GQster/catLaserPointer/SolidworksDesign/STLs/CatV2.1 - Base-1 - motor_arm-1.STL

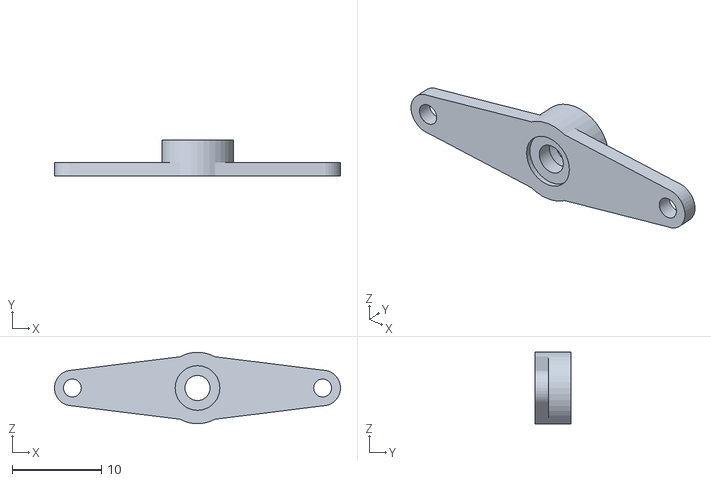
[picture p15: CAD file, 2021-12-10]
SolidworksDesign/STLs/CatV2.1 - Base-1 - motor_arm-1.STL
32.0 x 4.00 x 8.00
