GQster/catLaserPointer/SolidworksDesign/STLs/CatV2.1 - Base-1 - ControlArm-1.STL

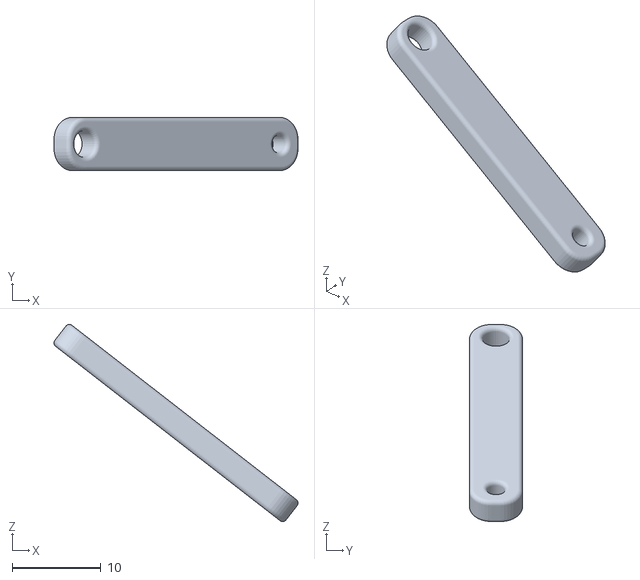
[picture p16: CAD file, 2021-12-10]
SolidworksDesign/STLs/CatV2.1 - Base-1 - ControlArm-1.STL
27.5 x 6.00 x 22.2
