GQster/catLaserPointer/SolidworksDesign/STLs/CatV2.1 - Base-1 - motor_arm-2.STL

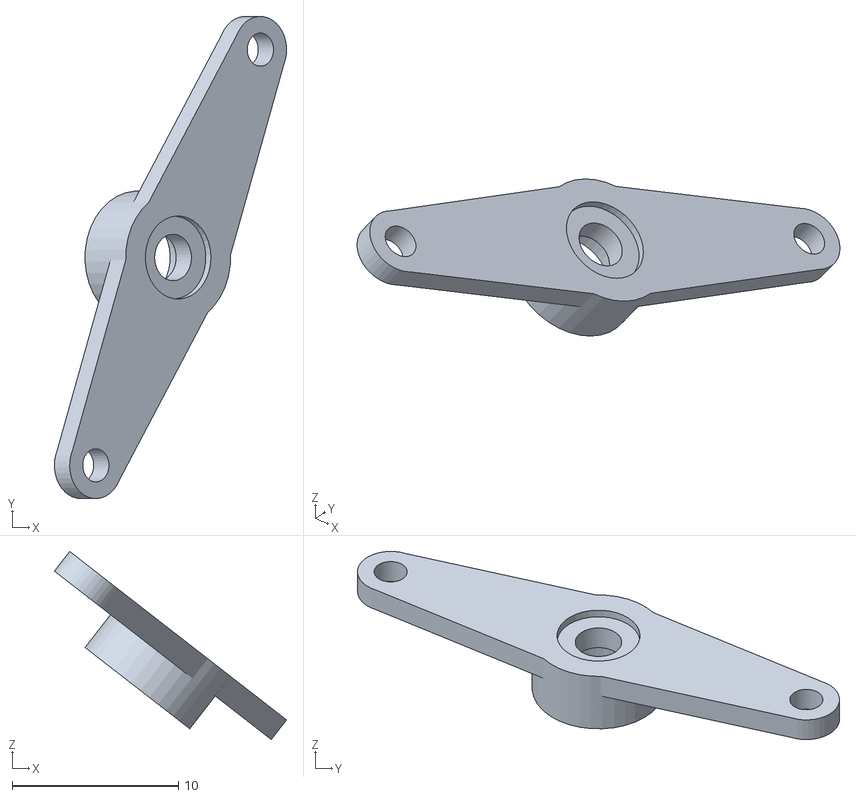
[picture p17: CAD file, 2021-12-10]
SolidworksDesign/STLs/CatV2.1 - Base-1 - motor_arm-2.STL
14.0 x 29.0 x 11.3
