GQster/catLaserPointer/SolidworksDesign/STLs/CatV2.1 - Base-1 - USB_CAM-1.STL

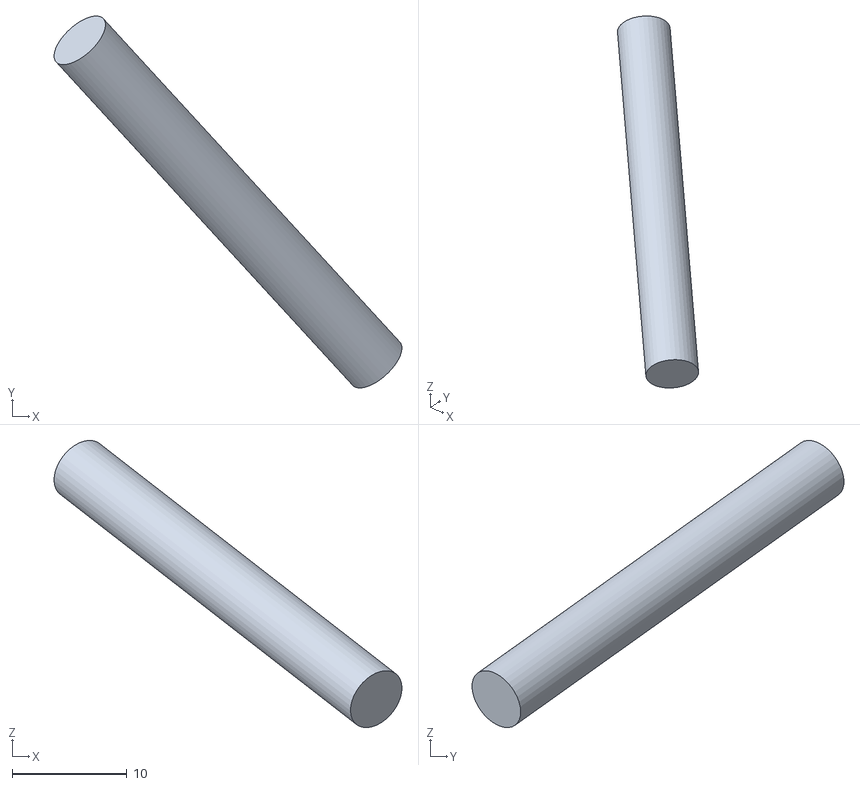
[picture p18: CAD file, 2021-12-10]
SolidworksDesign/STLs/CatV2.1 - Base-1 - USB_CAM-1.STL
30.3 x 32.4 x 25.0
